ElectronicCats/badge-bsides-sandiego-2025/firmware/bsides_badge/User/bitmaps.h

#pragma once

/**
 * Bitmaps must be flipped horizontally to be displayed correctly.
 */

// 'bsides_logo', 128x32px
static const unsigned char epd_bitmap_bsides_logo[] = {
    0x00, 0x00, 0x00, 0x00, 0x00, 0x00, 0x00, 0x00, 0x00, 0x00, 0x00, 0x00,
    0x00, 0x00, 0x00, 0x00, 0x00, 0x00, 0x00, 0x00, 0x00, 0x00, 0x00, 0x00,
    0x00, 0x00, 0x00, 0x00, 0x00, 0x00, 0x00, 0x00, 0x00, 0x00, 0x00, 0x00,
    0x00, 0x00, 0x00, 0x00, 0x00, 0x00, 0x00, 0x00, 0x00, 0x00, 0x00, 0x00,
    0x00, 0x00, 0x00, 0x00, 0x00, 0x00, 0x00, 0x00, 0x00, 0x03, 0x80, 0x00,
    0x00, 0x00, 0x00, 0x00, 0x00, 0x00, 0x00, 0x00, 0x00, 0x00, 0x00, 0x00,
    0x00, 0x0f, 0xf0, 0x03, 0xf8, 0x00, 0x00, 0x00, 0x00, 0x00, 0x00, 0x00,
    0x00, 0x00, 0x00, 0x00, 0x00, 0x3f, 0xfc, 0x0f, 0xf8, 0x00, 0x00, 0x00,
    0x00, 0x00, 0x00, 0x00, 0x00, 0x00, 0x00, 0x00, 0x00, 0x7f, 0xfe, 0x1e,
    0x18, 0x00, 0x00, 0x00, 0x00, 0x03, 0x9e, 0x7d, 0xf1, 0xc0, 0x44, 0x63,
    0xc0, 0xff, 0xfe, 0x1c, 0x1c, 0x00, 0x00, 0x00, 0x00, 0x04, 0x41, 0x04,
    0x42, 0x40, 0x4c, 0x90, 0x20, 0xf8, 0x1f, 0x0e, 0x1c, 0x00, 0x00, 0x00,
    0x00, 0x04, 0x41, 0x04, 0x44, 0x40, 0x5c, 0x90, 0x21, 0xf0, 0x0f, 0x07,
    0xfc, 0x00, 0x00, 0x00, 0x00, 0x04, 0x4d, 0x1c, 0x44, 0x40, 0x74, 0xf1,
    0xc1, 0xe0, 0x07, 0x87, 0xfc, 0x00, 0x00, 0x00, 0x00, 0x04, 0x51, 0x04,
    0x44, 0x40, 0x65, 0x0a, 0x03, 0xe0, 0x03, 0x87, 0x1e, 0x00, 0x00, 0x00,
    0x00, 0x04, 0x51, 0x04, 0x42, 0x40, 0x45, 0x0a, 0x03, 0xe1, 0x83, 0xc6,
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
    0x40, 0x00, 0x00, 0x00, 0x00, 0x6e, 0x16, 0x61, 0xdc, 0x31, 0xc4, 0x01,
    0x00, 0x18, 0x06, 0x00, 0xe0, 0x00, 0x00, 0x00, 0x00, 0x3c, 0x13, 0xc0,
    0xf8, 0x1f, 0x8c, 0x01, 0x80, 0x0e, 0x1c, 0x00, 0xe0, 0x00, 0x00, 0x00,
    0x00, 0x00, 0x00, 0x00, 0x00, 0x00, 0x00, 0x00, 0x00, 0x03, 0xf0, 0x00,
    0xe0, 0x00, 0x00, 0x00, 0x00, 0x00, 0x00, 0x00, 0x00, 0x00, 0x00, 0x00,
    0x00, 0x00, 0x00, 0x00, 0xe0, 0x00, 0x00, 0x00, 0x00, 0x00, 0x00, 0x00,
    0x00, 0x00, 0x00, 0x00, 0x00, 0x00, 0x00, 0x00, 0xe0, 0x00, 0x00, 0x00,
    0x00, 0x00, 0x00, 0x00, 0x00, 0x00, 0x00, 0x00, 0x00, 0x00, 0x00, 0x00,
    0xe0, 0x00, 0x00, 0x00, 0x00, 0x00, 0x00, 0x00, 0x00, 0x00, 0x00, 0x00,
    0x00, 0x00, 0x00, 0x00, 0xe0, 0x00, 0x00, 0x00, 0x00, 0x00, 0x00, 0x00,
    0x00, 0x00, 0x00, 0x00, 0x00, 0x00, 0x00, 0x00, 0xe0, 0x00, 0x00, 0x00,
    0x00, 0x00, 0x00, 0x00, 0x00, 0x00, 0x00, 0x00, 0x00, 0x00, 0x00, 0x00,
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

static const unsigned char* menus_bitmaps[3] = {
    epd_bitmap_menu_1, epd_bitmap_menu_2, epd_bitmap_menu_3};
