ElectronicCats/badge-bsides-sandiego-2025/firmware/bsides_badge/User/spritebank.h

//         >>>>>  T-I-N-Y  T-R-I-S v3 for ATTINY85  GPL v3 <<<<<
//                     Programmer: Daniel C 2019-2021
//              Contact EMAIL: electro_l.i.b@tinyjoypad.com
//                      https://WWW.TINYJOYPAD.COM
//           https://sites.google.com/view/arduino-collection

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
//  2023 modified to work with CH32V003 by Stefan Wagner:
//  github.com/wagiminator.

#pragma once

#include <stdint.h>

#ifdef __cplusplus
extern "C" {
#endif

const uint8_t H_Grid_TTTRIS[] = {
    0, 0, 0, 1, 1, 1, 2, 2, 2, 3, 3,  3,  4,  4,  4,  5,  5,  5,  6, 6,
    6, 7, 7, 7, 8, 8, 8, 9, 9, 9, 10, 10, 10, 11, 11, 11, 12, 12, 12};

const uint8_t Pieces_TTRIS[] = {
    // 0
    0b00000000, 0b00100000, 0b01110000, 0b00000000, 0b00000000,
    // 1
    0b00000000, 0b00000000, 0b00110000, 0b00110000, 0b00000000,
    // 2
    0b00000000, 0b00000000, 0b00110000, 0b01100000, 0b00000000,
    // 3
    0b00000000, 0b00010000, 0b00110000, 0b00100000, 0b00000000,
    // 4
    0b00100000, 0b00100000, 0b00100000, 0b00100000, 0b00000000,
    // 5
    0b00000000, 0b00100000, 0b00100000, 0b01100000, 0b00000000,
    // 6
    0b00000000, 0b00100000, 0b00100000, 0b00110000, 0b00000000};

const uint8_t tiny_PREVIEW_block_TTTRIS[] = {2, 1, 0b11000000, 0b11000000};

const uint8_t tinyblock_TTTRIS[] = {3, 1, 0x07, 0x05, 0x07};

const uint8_t tinyblock2_TTTRIS[] = {3, 1, 0b11100000, 0b11100000, 0b11100000};

const uint8_t police_TTRIS[] = {
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
    0x77, 0x55, 0xDD, 0x55, 0x77, 0xFF, 0x00, 0x00, 0xFF, 0x00, 0x00, 0x00,
    0x00, 0x00, 0x00, 0x00, 0x00, 0x00, 0x00, 0x00, 0x00, 0x00, 0x00, 0x00,
    0x00, 0x00, 0x00, 0x00, 0x00, 0x00, 0x00, 0x00, 0x00, 0x00, 0x00, 0x00,
    0x00, 0x00, 0x00, 0x00, 0x00, 0x00, 0x00, 0x00, 0x00, 0x00, 0x00, 0xFF,
    0x00, 0x00, 0xFF, 0x00, 0xFE, 0xFD, 0x07, 0x03, 0x03, 0x03, 0x03, 0x03,
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

#ifdef __cplusplus
};
#endif
