ElectronicCats/badge-bsides-sandiego-2025/firmware/bsides_badge/SSD1306/bomb.c

#include "include/bomb.h"

/*
The bomb illustration has been drawn and provided by
[DoubleWaffleCakes](https://www.reddit.com/user/DoubleWaffleCakes/).
*/
const unsigned char bomb_i_stripped[] = {
    0x00, 0x00, 0x00, 0x00, 0x00, 0x00, 0x00, 0x00, 0x00, 0x00, 0x00, 0x00,
    0x00, 0x00, 0x00, 0x00, 0x00, 0x00, 0x00, 0x00, 0x00, 0x00, 0x0c, 0x00,
    0x00, 0x00, 0x12, 0x00, 0x00, 0x00, 0x24, 0x00, 0x00, 0x00, 0x48, 0x00,
    0x00, 0x00, 0x50, 0x00, 0x00, 0x00, 0xf8, 0x00, 0x00, 0x03, 0xfe, 0x00,
    0x00, 0x0f, 0xff, 0x80, 0x00, 0x1f, 0xff, 0xc0, 0x00, 0x1f, 0xff, 0xc0,
    0x00, 0x3f, 0xff, 0xe0, 0x00, 0x3f, 0xff, 0xe0, 0x00, 0x73, 0x9f, 0xf0,
    0x00, 0x73, 0x9f, 0xf0, 0x00, 0x73, 0x9f, 0xf0, 0x00, 0x73, 0x9f, 0xf0,
    0x00, 0x73, 0x9f, 0xf0, 0x00, 0x3f, 0xff, 0xe0, 0x00, 0x3f, 0xff, 0xe0,
    0x00, 0x1f, 0xff, 0xc0, 0x00, 0x1f, 0xff, 0xc0, 0x00, 0x0f, 0xff, 0x80,
    0x00, 0x13, 0xe0, 0x40, 0x00, 0x20, 0xc0, 0x20, 0x00, 0x7f, 0xff, 0xe0,
    0x00, 0x00, 0x00, 0x00, 0x00, 0x00, 0x00, 0x00};

const unsigned int bomb_i_stripped_len = 128;
