ElectronicCats/badge-bsides-sandiego-2025/firmware/bsides_badge/SSD1306/include/bomb.h

#ifndef _BOMB_H
#define _BOMB_H

/*
The bomb illustration has been drawn and provided by
[DoubleWaffleCakes](https://www.reddit.com/user/DoubleWaffleCakes/).
*/
extern const unsigned char bomb_i_stripped[];

extern const unsigned int bomb_i_stripped_len;

#endif
