ElectronicCats/badge-bsides-sandiego-2025/firmware/bsides_badge/User/hardware_tests.h

#pragma once

/**
 * @brief Run hardware tests
 * This function runs a series of tests to verify that the following hardware
 * components are working correctly:
 * - Buttons
 * - LEDs
 * - OLED display
 *
 * @return void
 */
void hardware_tests_start();
